omer38/Discrete-OPAMP/Draft1.asc

C1: cap; 470p
C2: cap; 470p
D1: diode; 1N4148
D2: diode; 1N4148
D3: diode; 1N4148
D4: diode; 1N4148
Q1: pnp; 2N3906
Q2: pnp; 2N3906
Q3: npn; 2N3904
Q4: npn; 2N3904
Q5: pnp; 2N3906
Q6: npn; 2N3904
Q7: pnp; 2N3906
Q8: pnp; 2N3906
Q9: pnp; 2N3906
Q10: npn; 2N3904
Q11: npn; 2N3904
Q12: pnp; 2N3906
Q13: npn; 2N3904
Q14: pnp; 2N3906
R1: res; 16k
R2: res; 5k
R3: res; 10
R4: res; 16.5k
R5: res; 150k
R6: res; 150k
R7: res; 1Meg
R8: res; 16k
R10: res; 10
R11: res; 16.5k
R12: res; 150k
R13: res; 150k
R14: res; 5k
R: res; 5k
V1: voltage; 10
V2: voltage; SINE(0 10m 1k)
V3: voltage; -10
V4: voltage; 10
V5: voltage; SINE(0 3 1k)
V6: voltage; -10
Named nets: 0, Vin, Vout, Vin2, Vout2
.tran 0 40ms 30ms
Selin - Ömer --EE313  Project - Differential OPAMP Design
Stage 1: Differential Amplifier with Current Mirror on the Top
Stage 2: Gain and Level Shifter
Stage 3: Push-Pull Voltage Buffer
;tran 0 40ms 30ms
Stage 1: Differential Amplifier
Stage 2: Gain
Stage 3: Push-Pull Voltage Buffer
Test Circuit
